AESilky/sd-zmb/hw/SD-ZMB/Docs/CLK_to_CLK2-IOop-timing.PDF

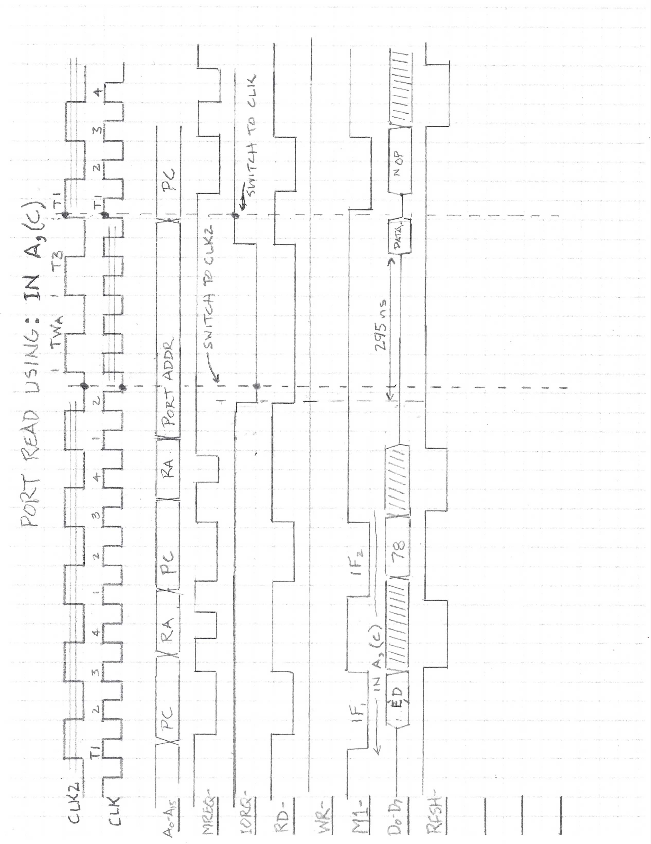
[picture p2: page 1]
