AESilky/sd-zmb/hw/SD-ZMB/Docs/CLK_to_CLK2-timing.PDF

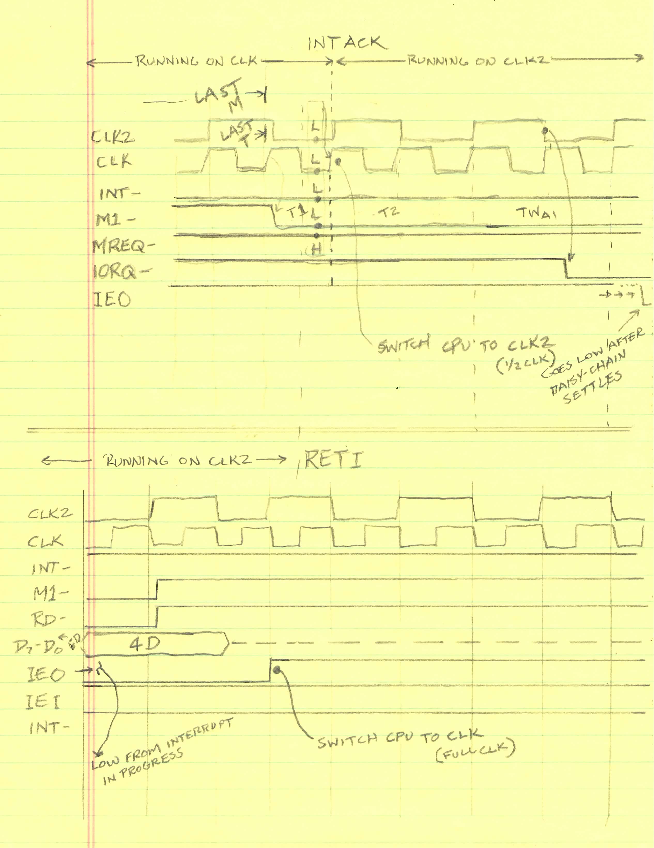
[picture p3: page 1]
