AESilky/sd-zmb/hw/SD-ZMB/Docs/Z80-INTACK-6vs12MHz-AddWS.pdf

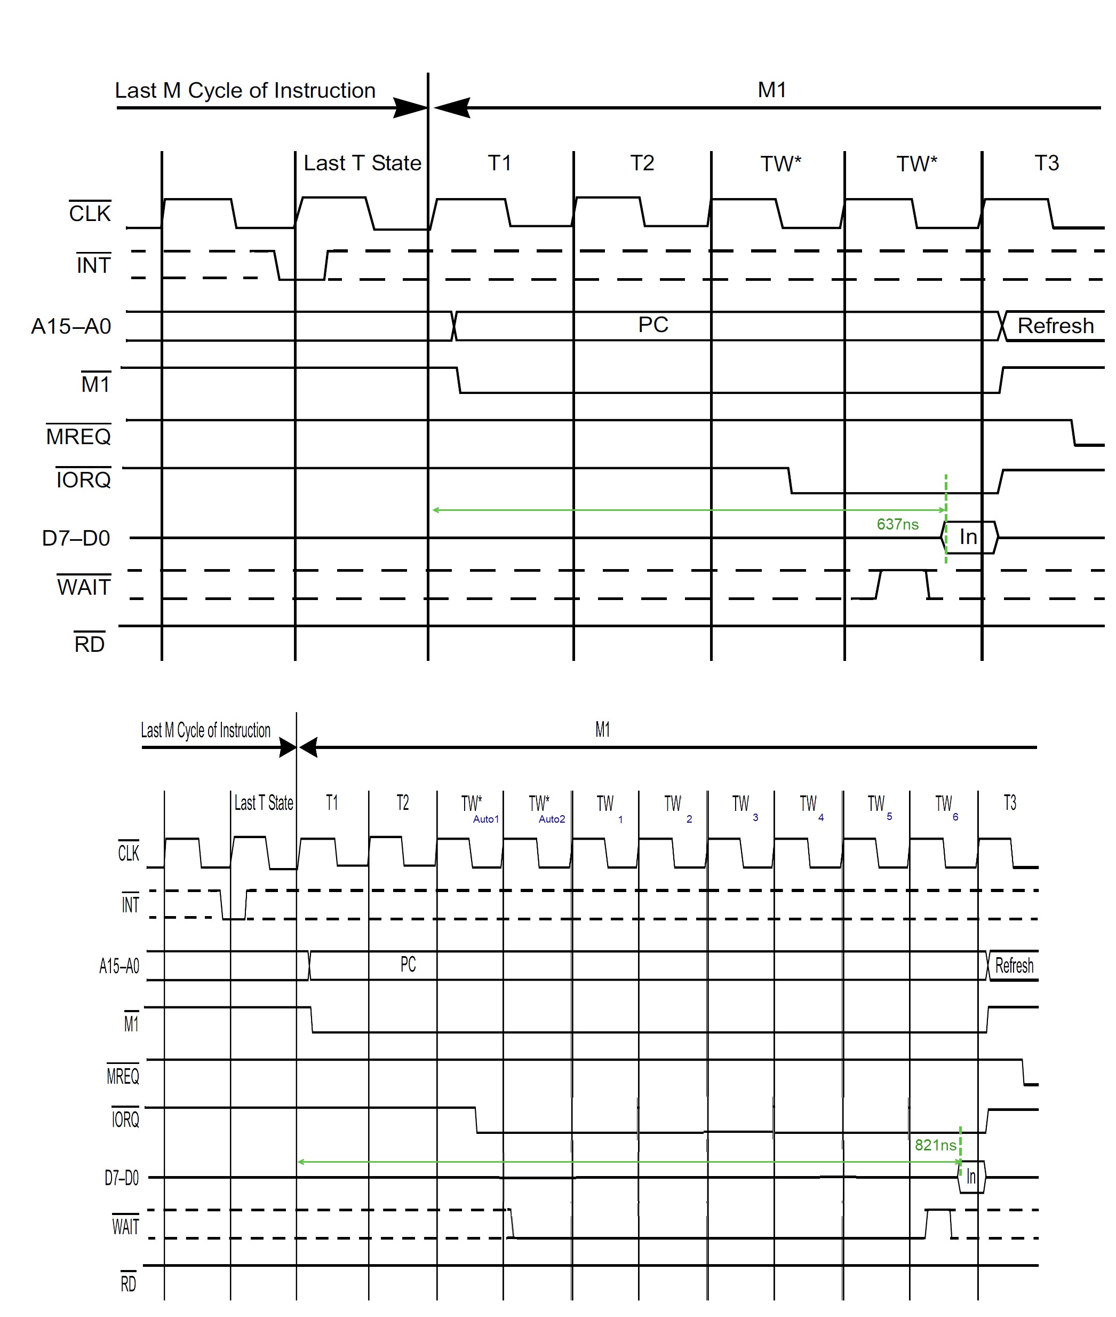
[picture p4: page 1]
