AESilky/sd-zmb/hw/SD-ZMB/Docs/Z80-IO-6vs12MHz-AddWS.pdf

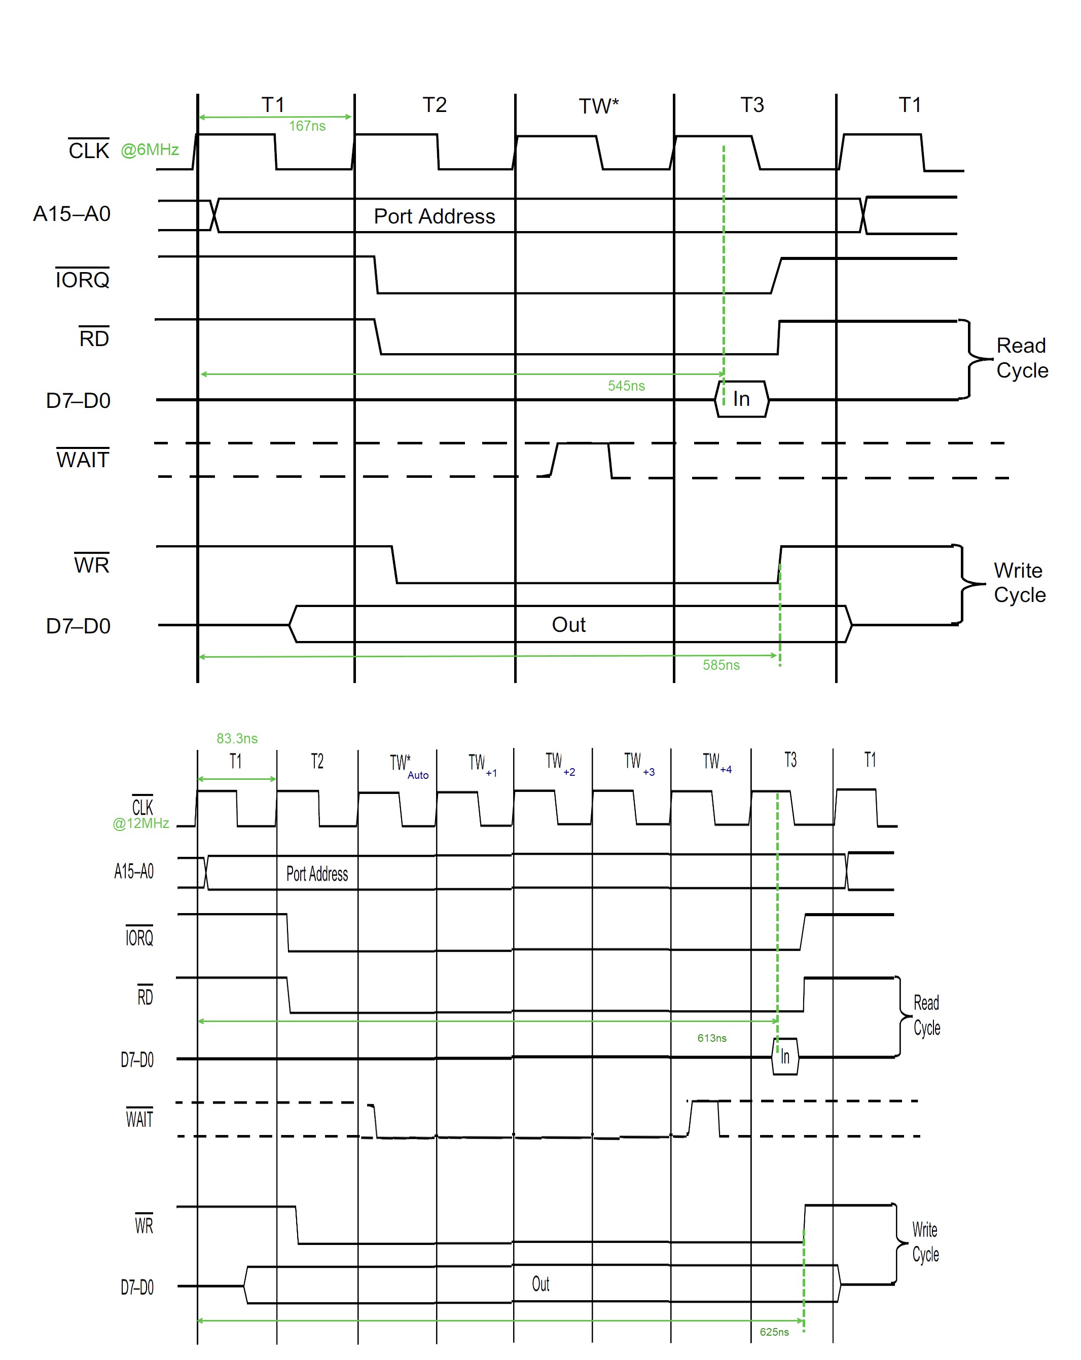
[picture p5: page 1]
