AESilky/sd-zmb/hw/SD-ZMB/Docs/Z80-IO-timing-ws.pdf

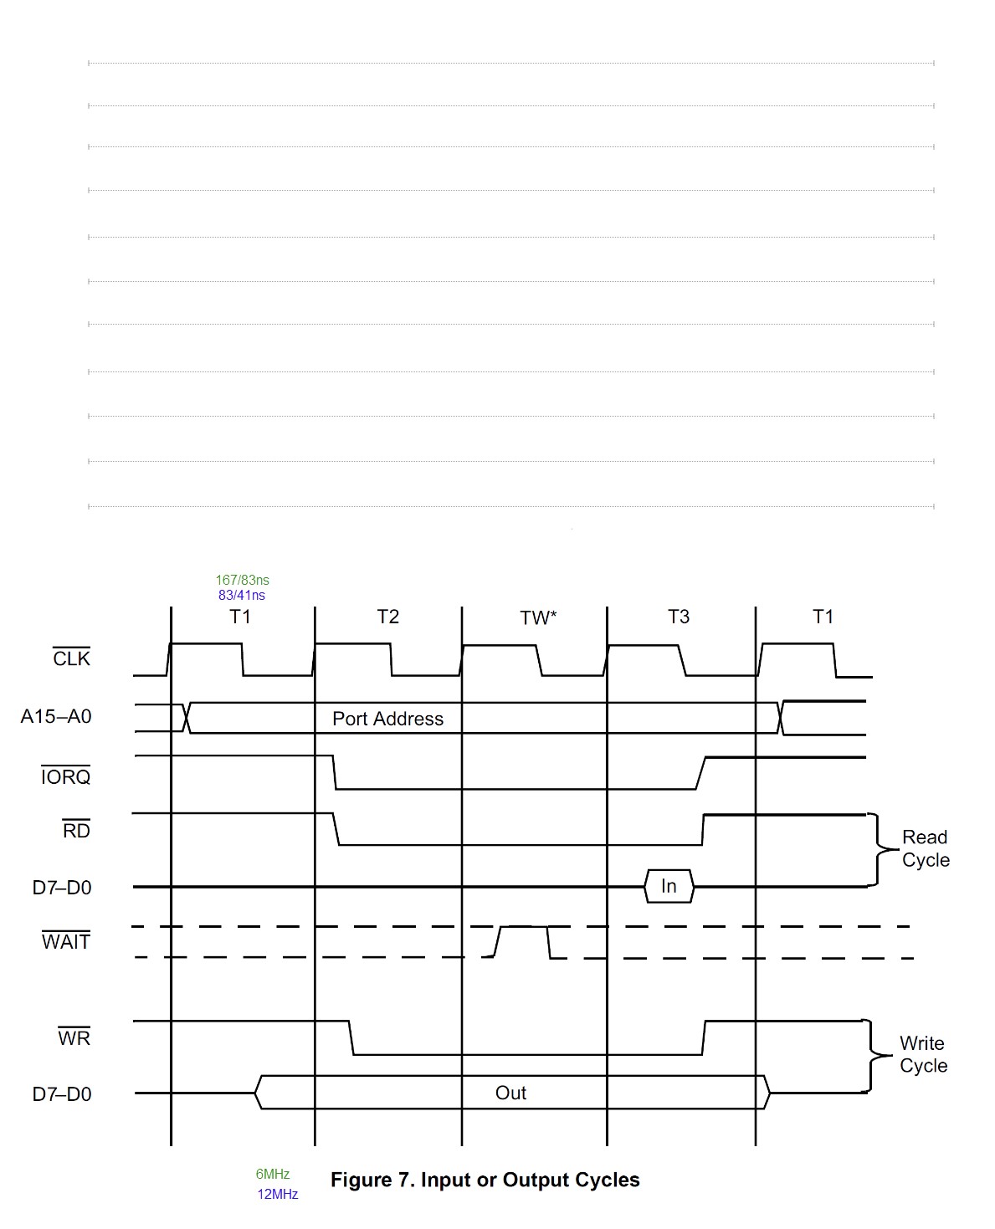
[picture p6: page 1]
