AESilky/sd-zmb/hw/SD-ZMB/Plot/SD-MSZ.pdf

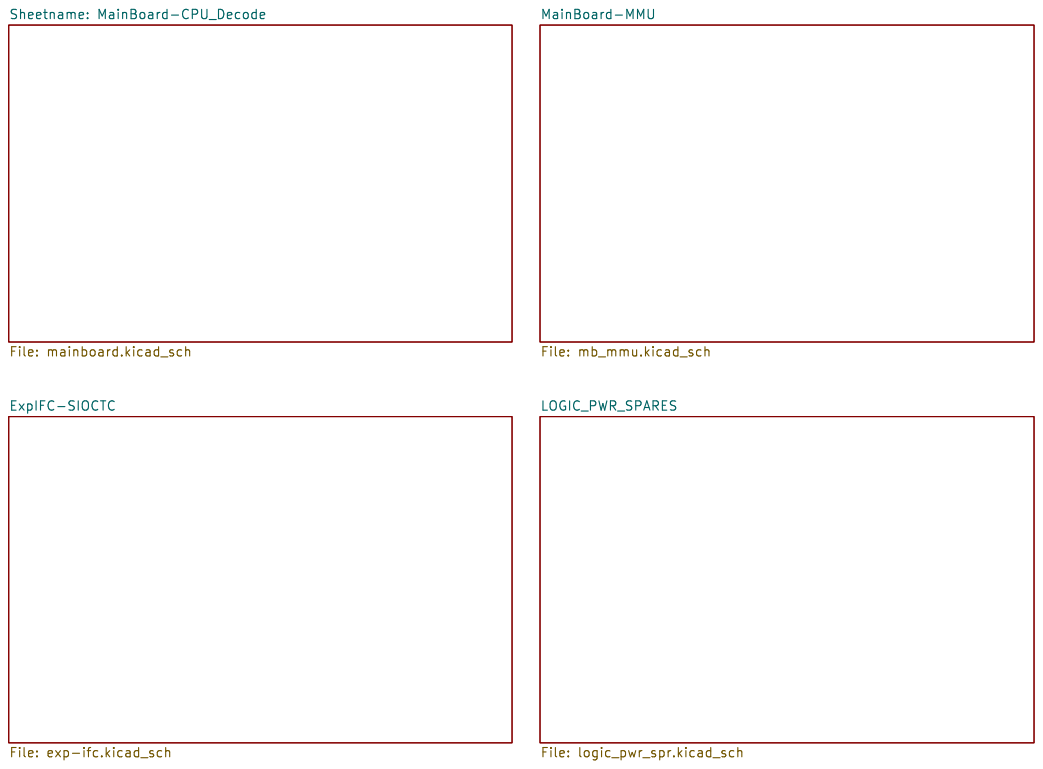
[picture p18: page 1]

File: SD-MSZ.kicad_sch Sheet: / SilkyDESIGN

Id: 1/5 Title: MicroSystem Z80 w/Front Panel & RC2014 Bus

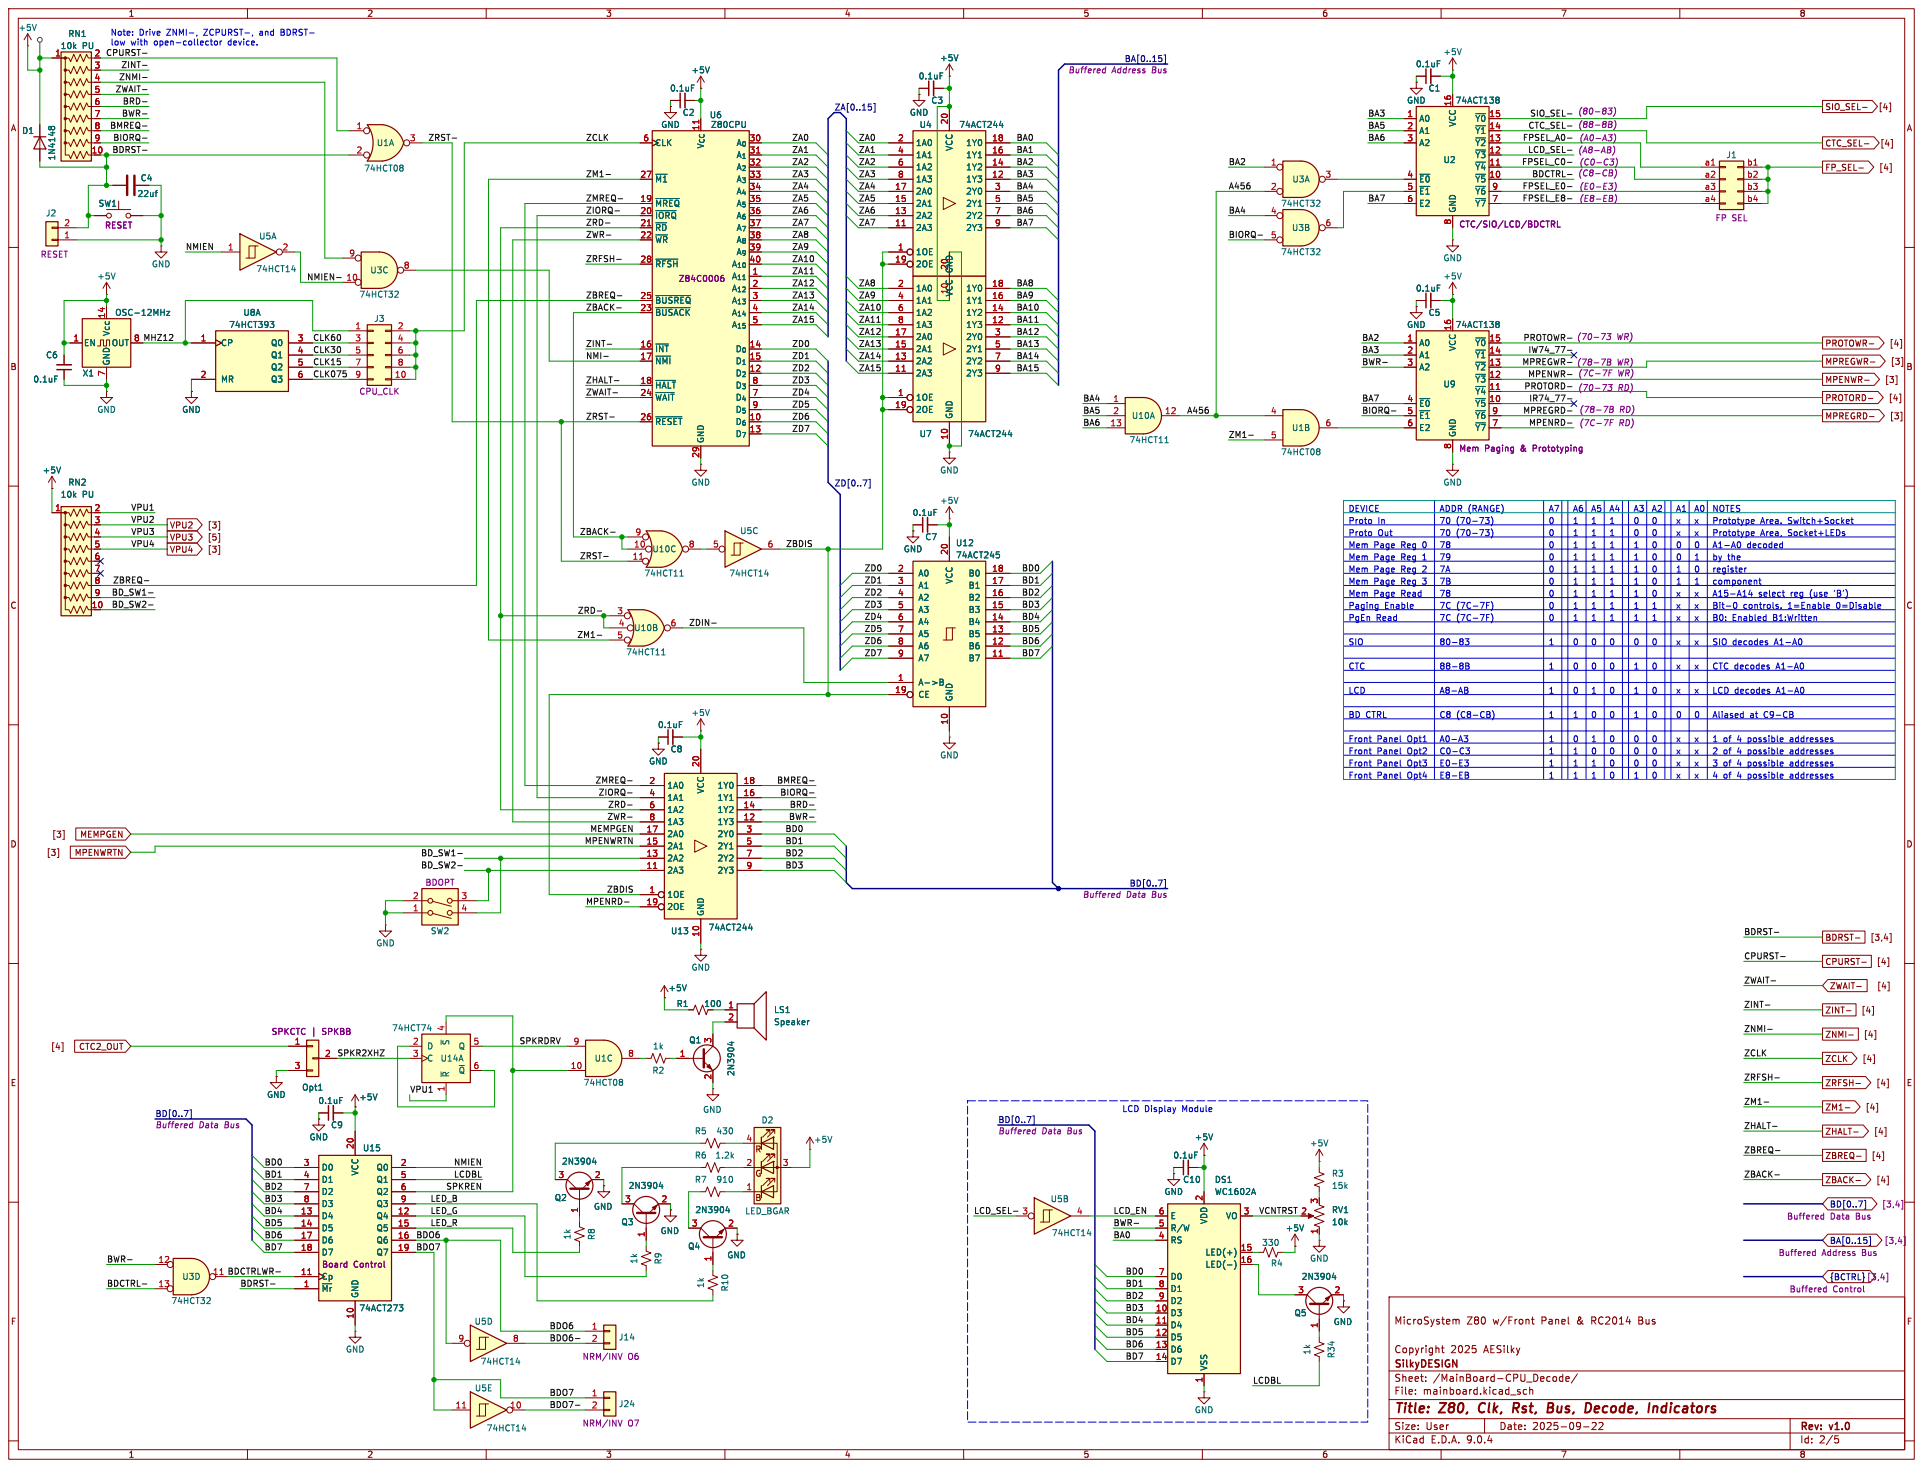
[picture p19: page 2]

74ACT138 CTC/SIO/LCD/BDCTRL +5V

8 ~{Y0}15 ~{Y1}14 ~{Y2}13 ~{Y3}12 ~{Y4}11 ~{Y5}10 ~{Y6}9 ~{Y7}7 X1 OSC-12MHz EN 1 Vcc 14 GND

ZWAIT- ZRST- NMI- ZHALT-

BD7 BD5 BD[0..7] Buffered Data Bus BD5 BD4

BD2 BD[0..7] Buffered Data Bus

SilkyDESIGN
File: mainboard.kicad_sch Sheet: /MainBoard-CPU_Decode/
Id: 2/5 Title: Z80, Clk, Rst, Bus, Decode, Indicators

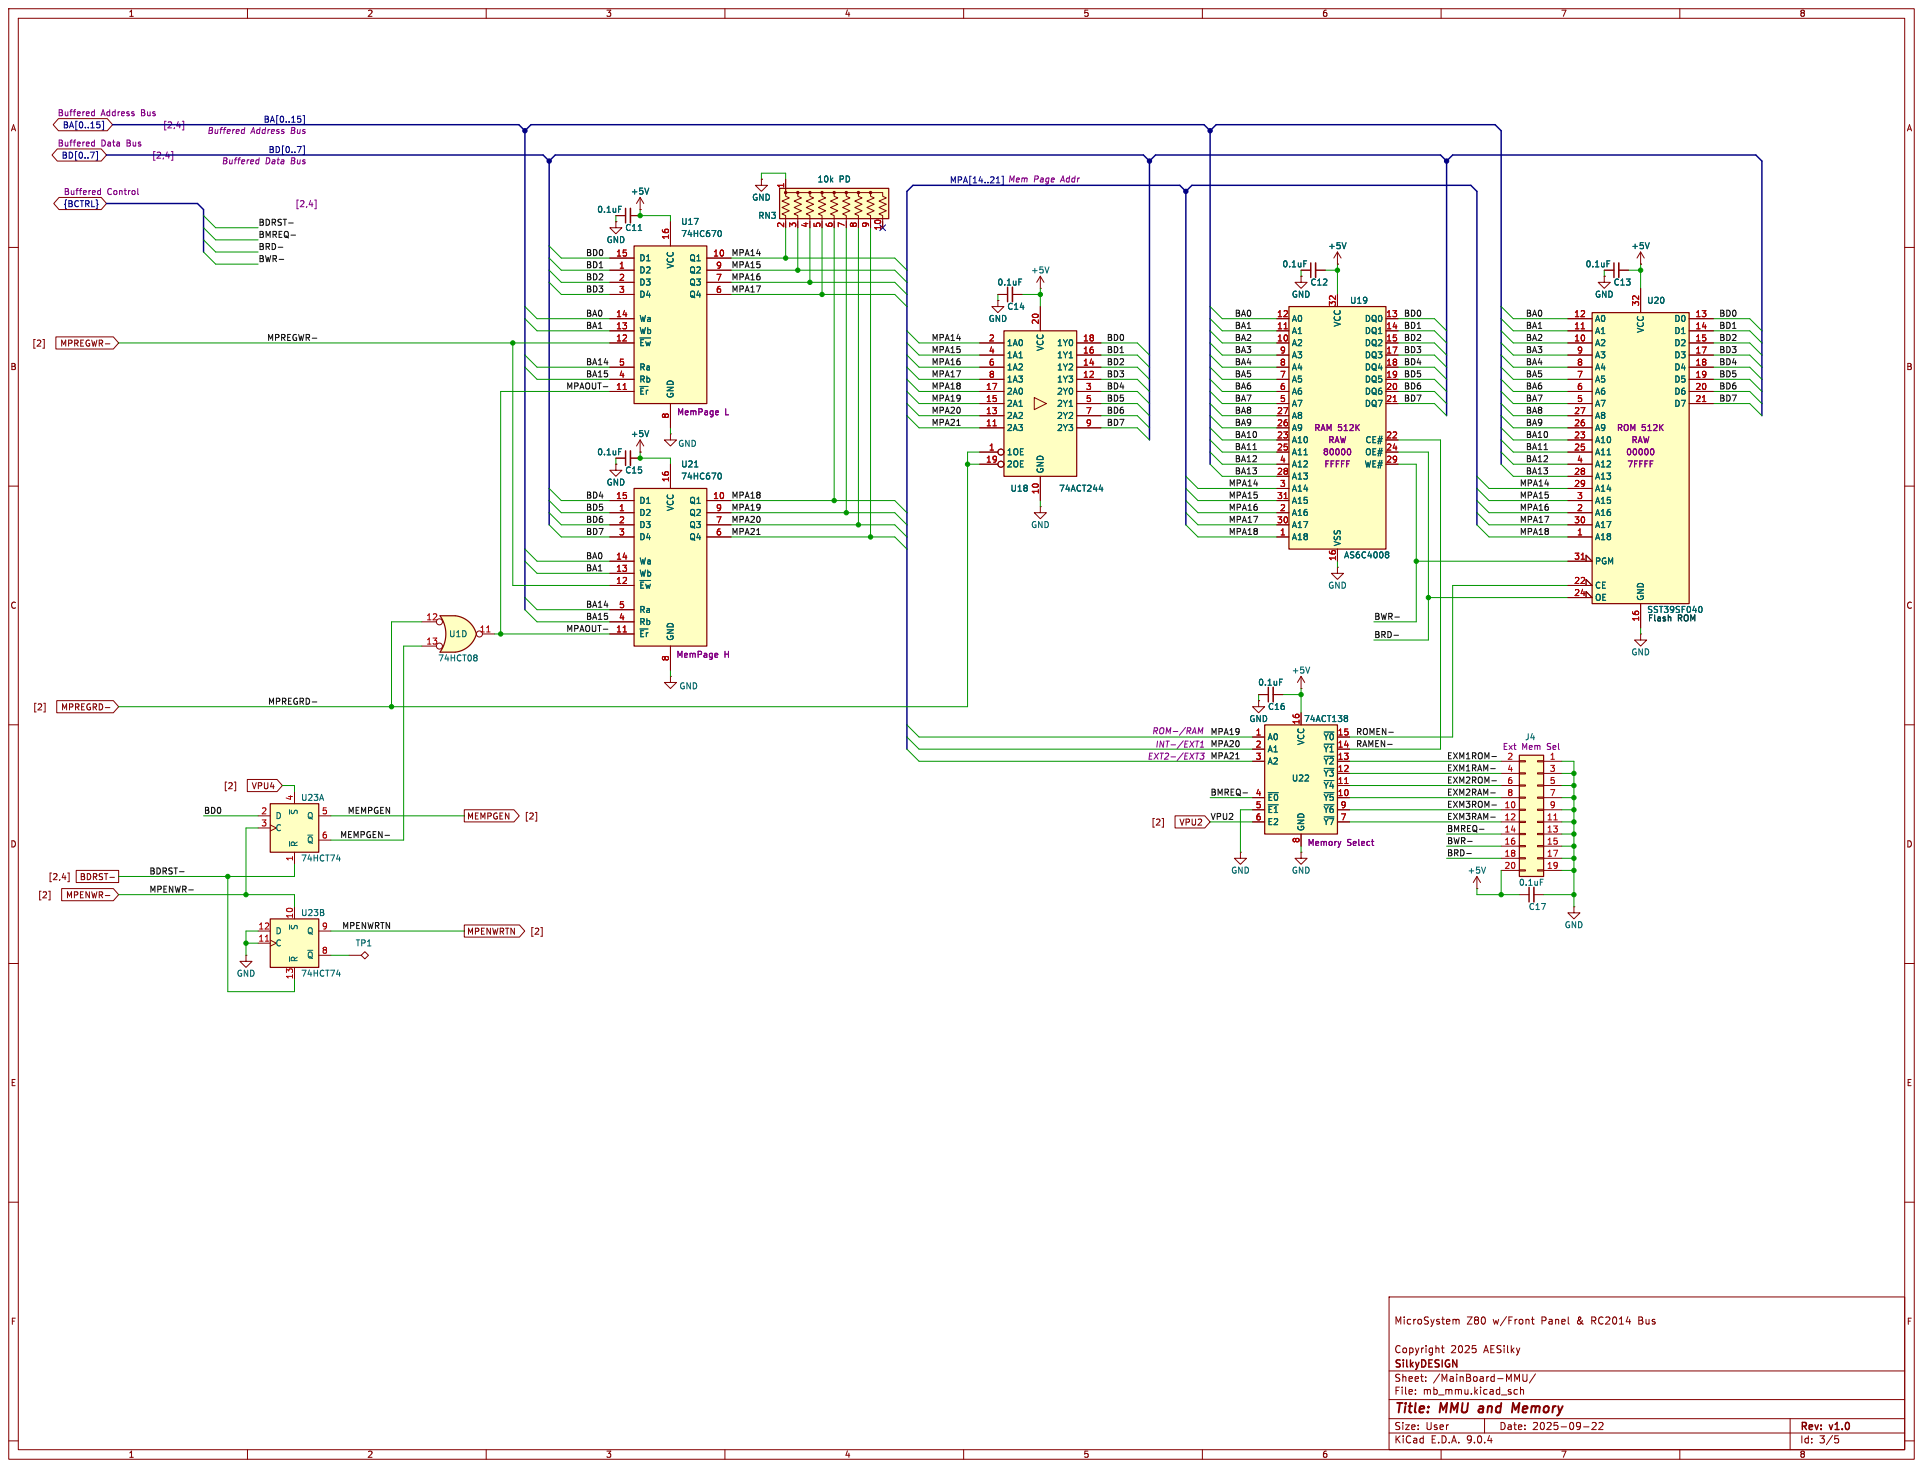
[picture p20: page 3]

MPREGWR- BA[0..15] Buffered Address Bus

File: mb_mmu.kicad_sch Sheet: /MainBoard-MMU/ SilkyDESIGN

Id: 3/5 Title: MMU and Memory

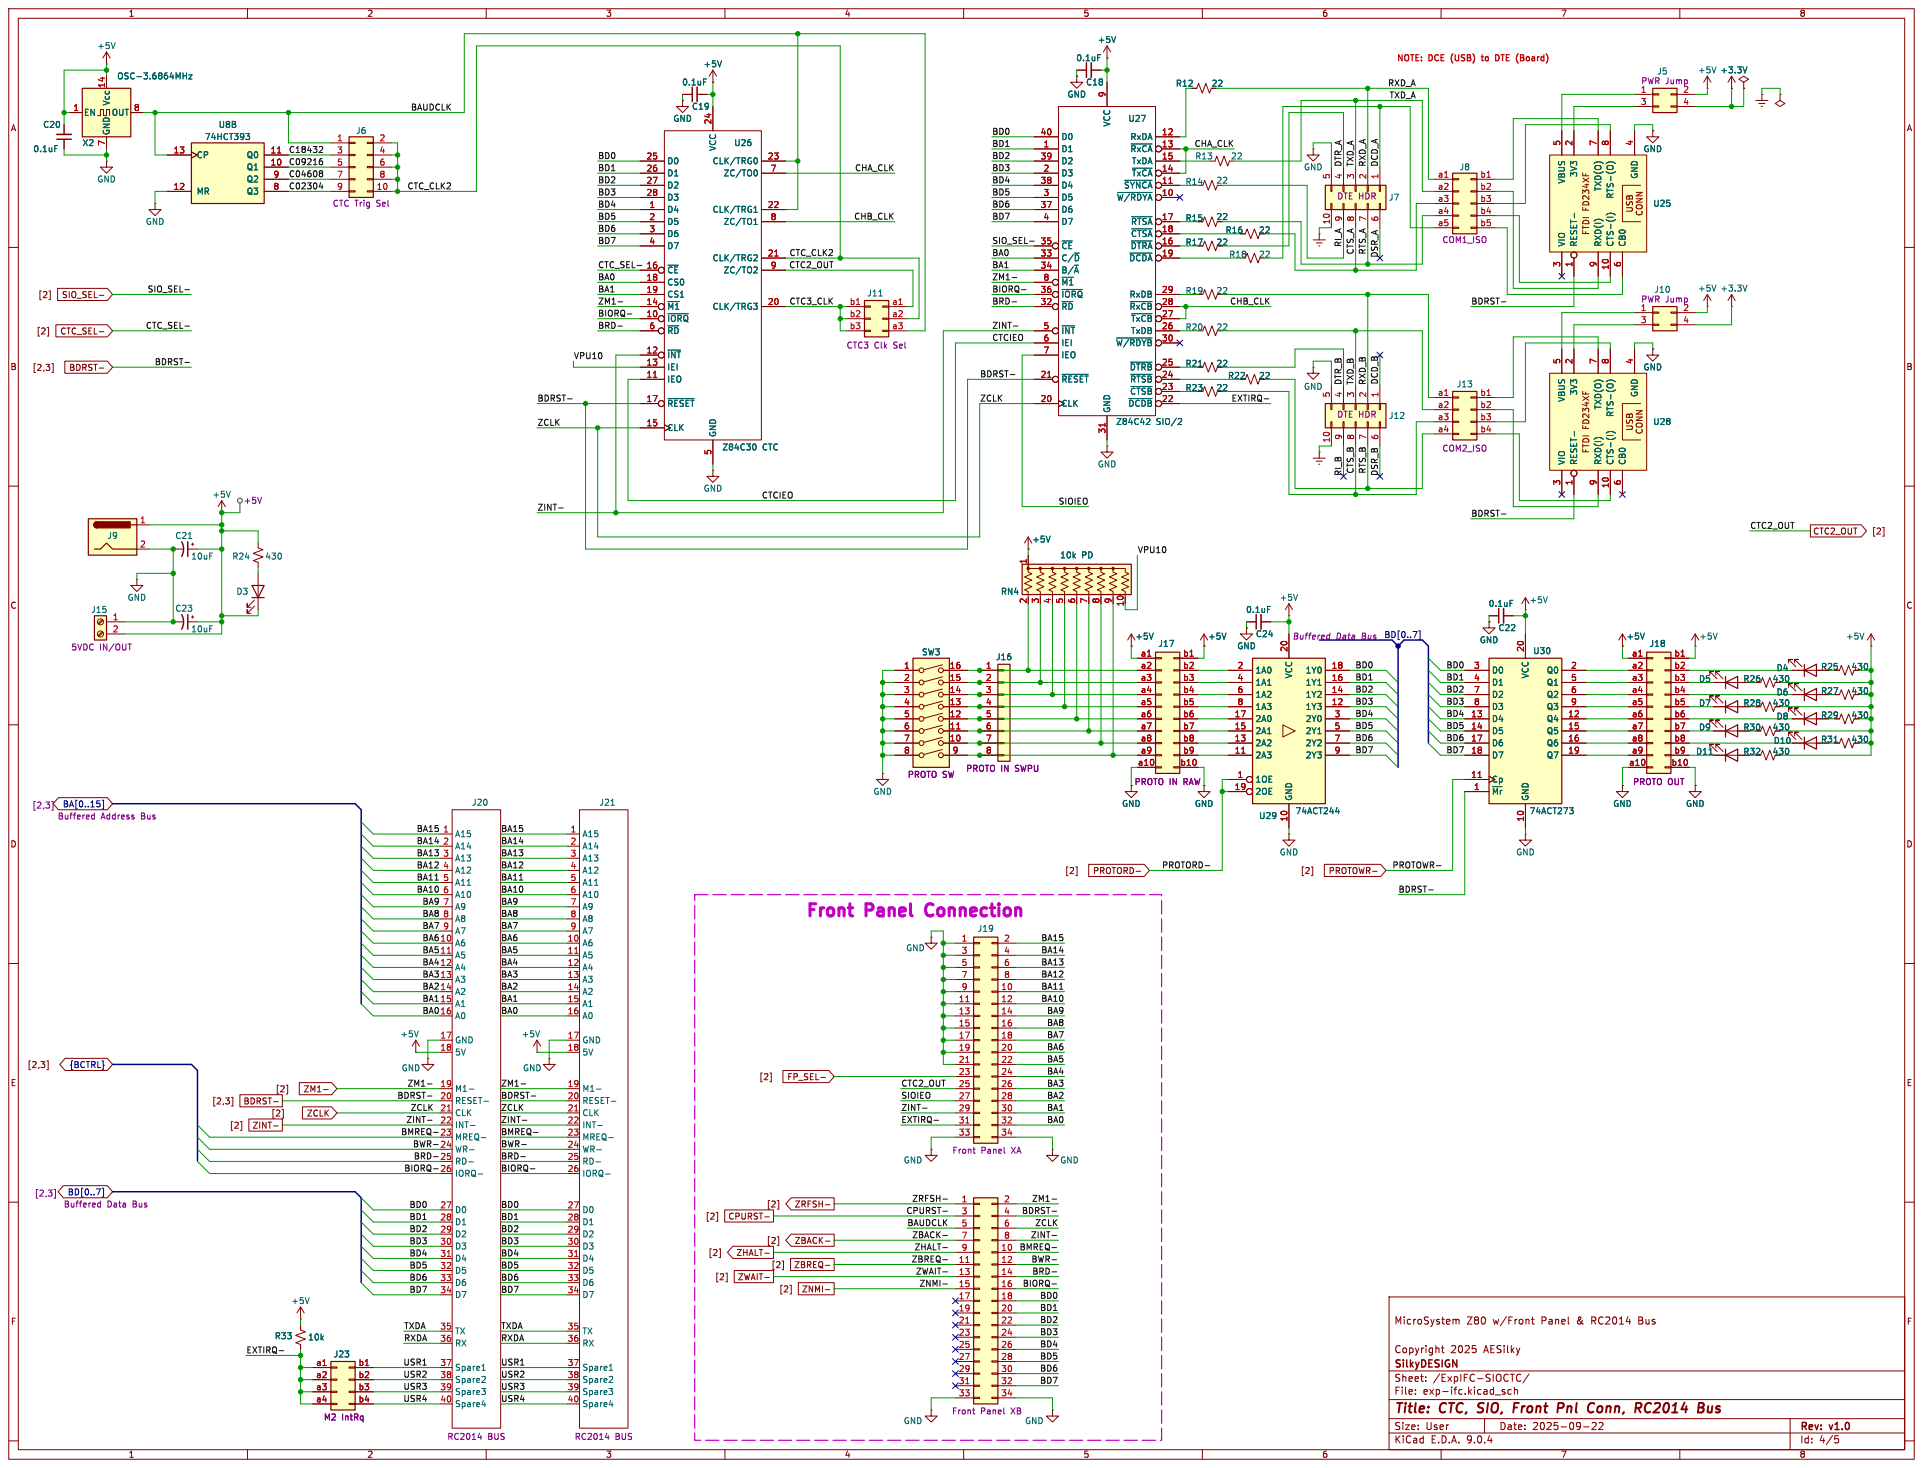
[picture p21: page 4]

NOTE: DCE (USB) to DTE (Board)

9 GND 31 RxDA 12 ~{RxCA}13 TxDA 15 ~{TxCA}14 ~{SYNCA}11 ~{W/RDYA}10 ~{RTSA}17 ~{CTSA}18 ~{DTRA}16 ~{DCDA}19 RxDB 29 ~{RxCB}28 ~{TxCB}27 TxDB 26 ~{W/RDYB} 30 ~{DTRB}25 ~{RTSB}24 ~{CTSB}23 ~{DCDB}22 U27 Z84C42 SIO/2 GND FTDI FD234XF USB

9 GND 31 RxDA 12 ~{RxCA}13 TxDA 15 ~{TxCA}14 ~{SYNCA}11 ~{W/RDYA}10 ~{RTSA}17 ~{CTSA}18 ~{DTRA}16 ~{DCDA}19 RxDB 29 ~{RxCB}28 ~{TxCB}27 TxDB 26 ~{W/RDYB} 30 ~{DTRB}25 ~{RTSB}24 ~{CTSB}23 ~{DCDB}22 GND GND

5 CLK/TRG0 23 ZC/TO0 7 CLK/TRG1 22 ZC/TO1 8 CLK/TRG2 21 ZC/TO2 9 CLK/TRG3 20 U26 Z84C30 CTC

5 CLK/TRG0 23 ZC/TO0 7 CLK/TRG1 22 ZC/TO1 8 CLK/TRG2 21 ZC/TO2 9 CLK/TRG3 20 C22

Buffered Data Bus BD[0..7] BD1

BD6 BDRST- PROTOWR- BD5 BD4 BD3 ZINT- BWR- BDRST- ZCLK

[2] FP_SEL- BA[0..15] [2,3] Buffered Address Bus

INT- 22 MREQ- 23 WR- 24 RD- 25

SilkyDESIGN
File: exp-ifc.kicad_sch Sheet: /ExpIFC-SIOCTC/
Id: 4/5 Title: CTC, SIO, Front Pnl Conn, RC2014 Bus

34 Front Panel XB GND

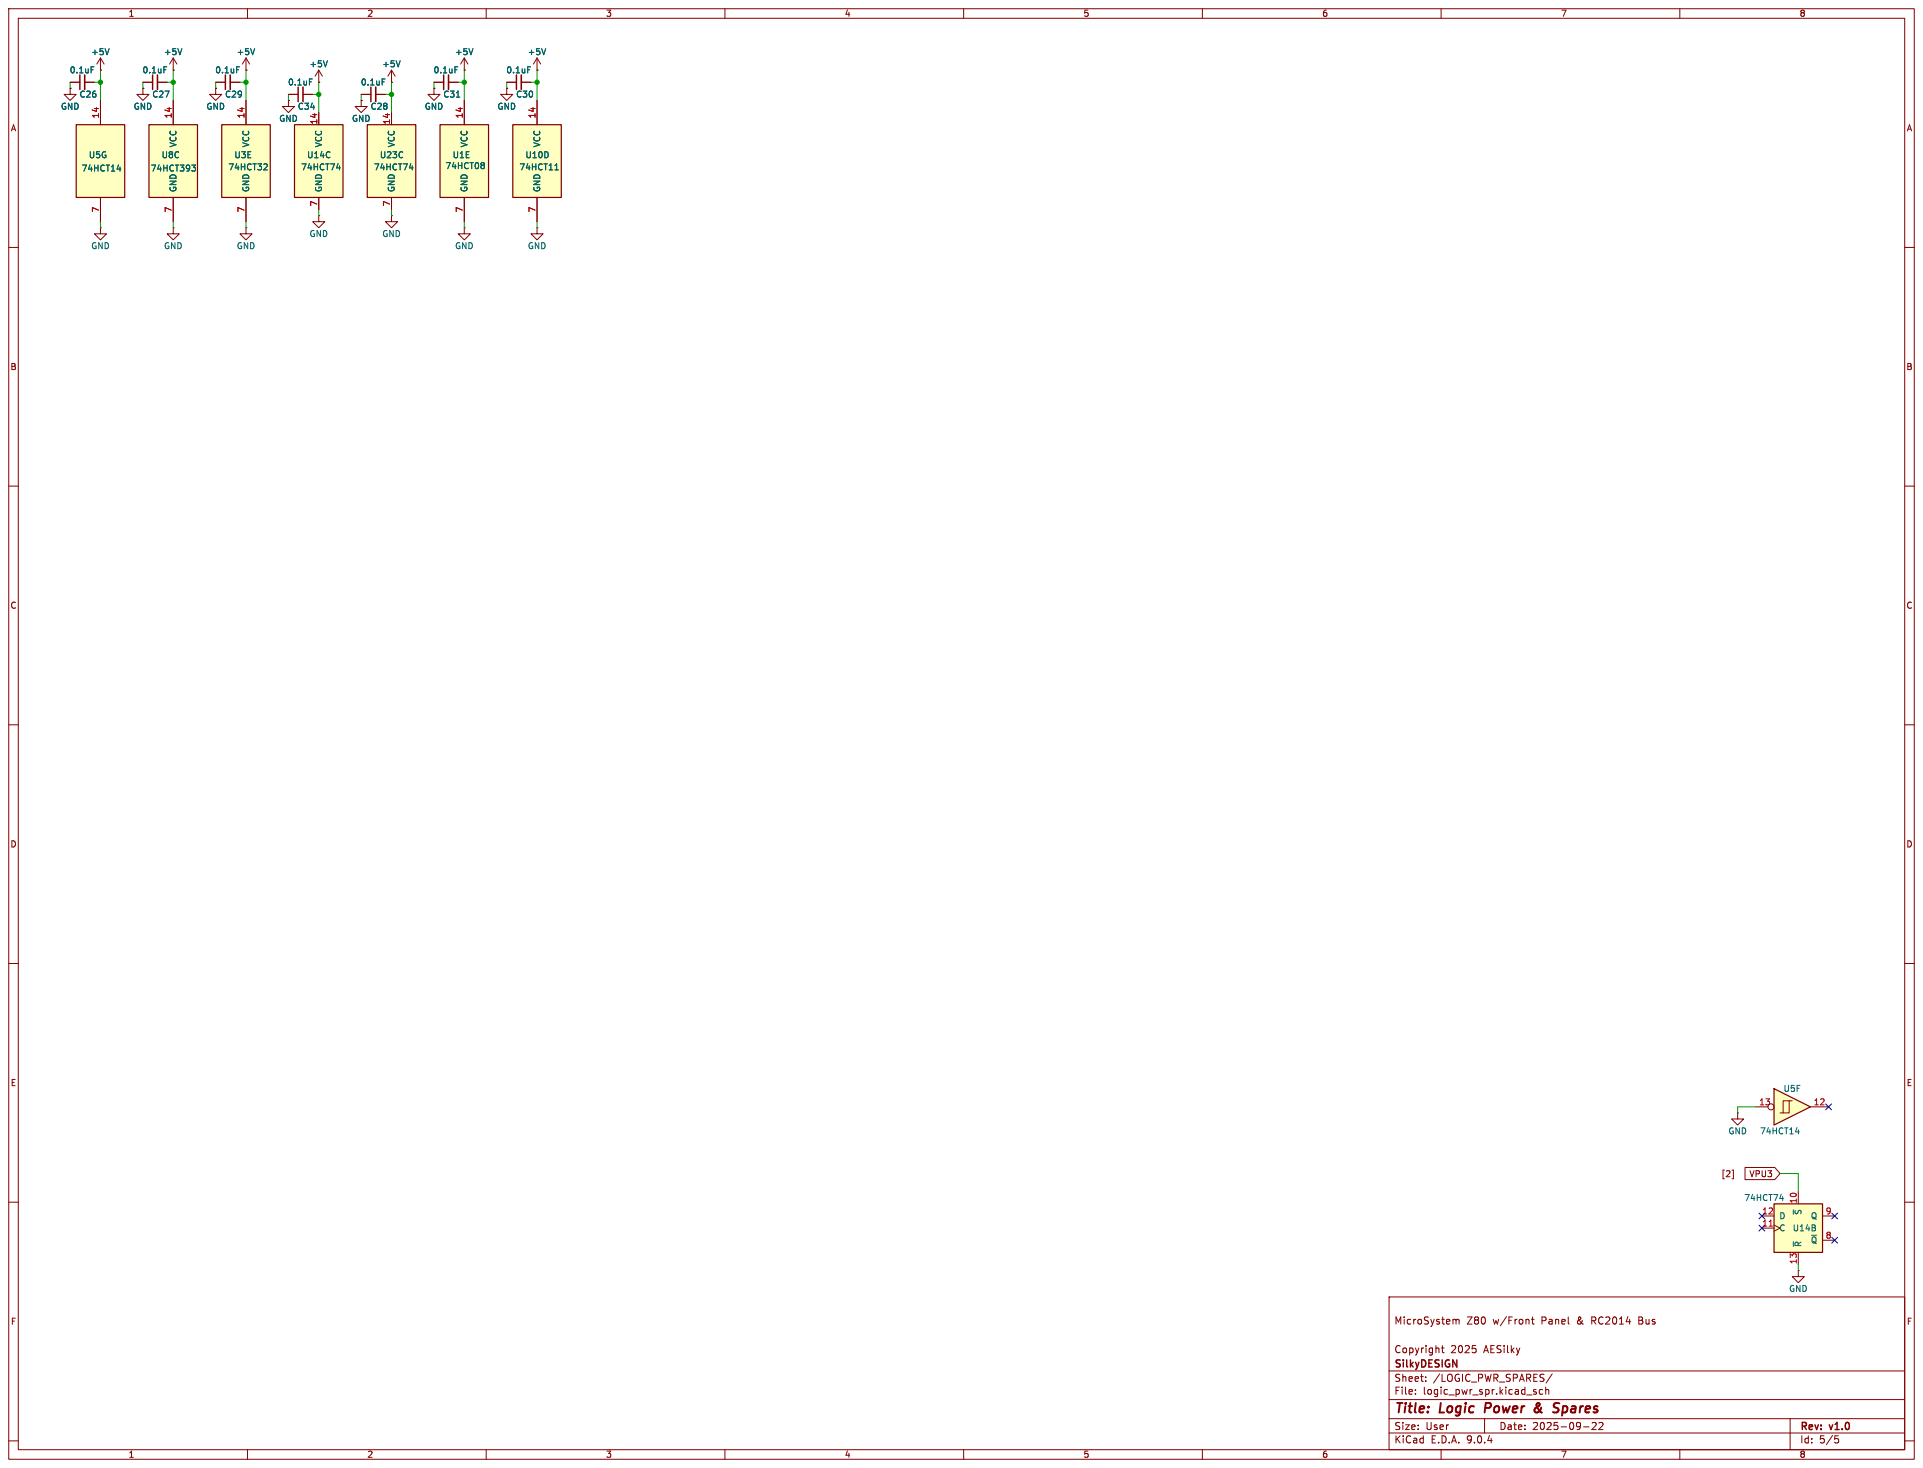
[picture p22: page 5]

SilkyDESIGN
File: logic_pwr_spr.kicad_sch Sheet: /LOGIC_PWR_SPARES/
Id: 5/5 Title: Logic Power & Spares
