AESilky/sd-zmb/hw/SD-ZMB/Plot/ZMB-PCB_PR8_2.pdf

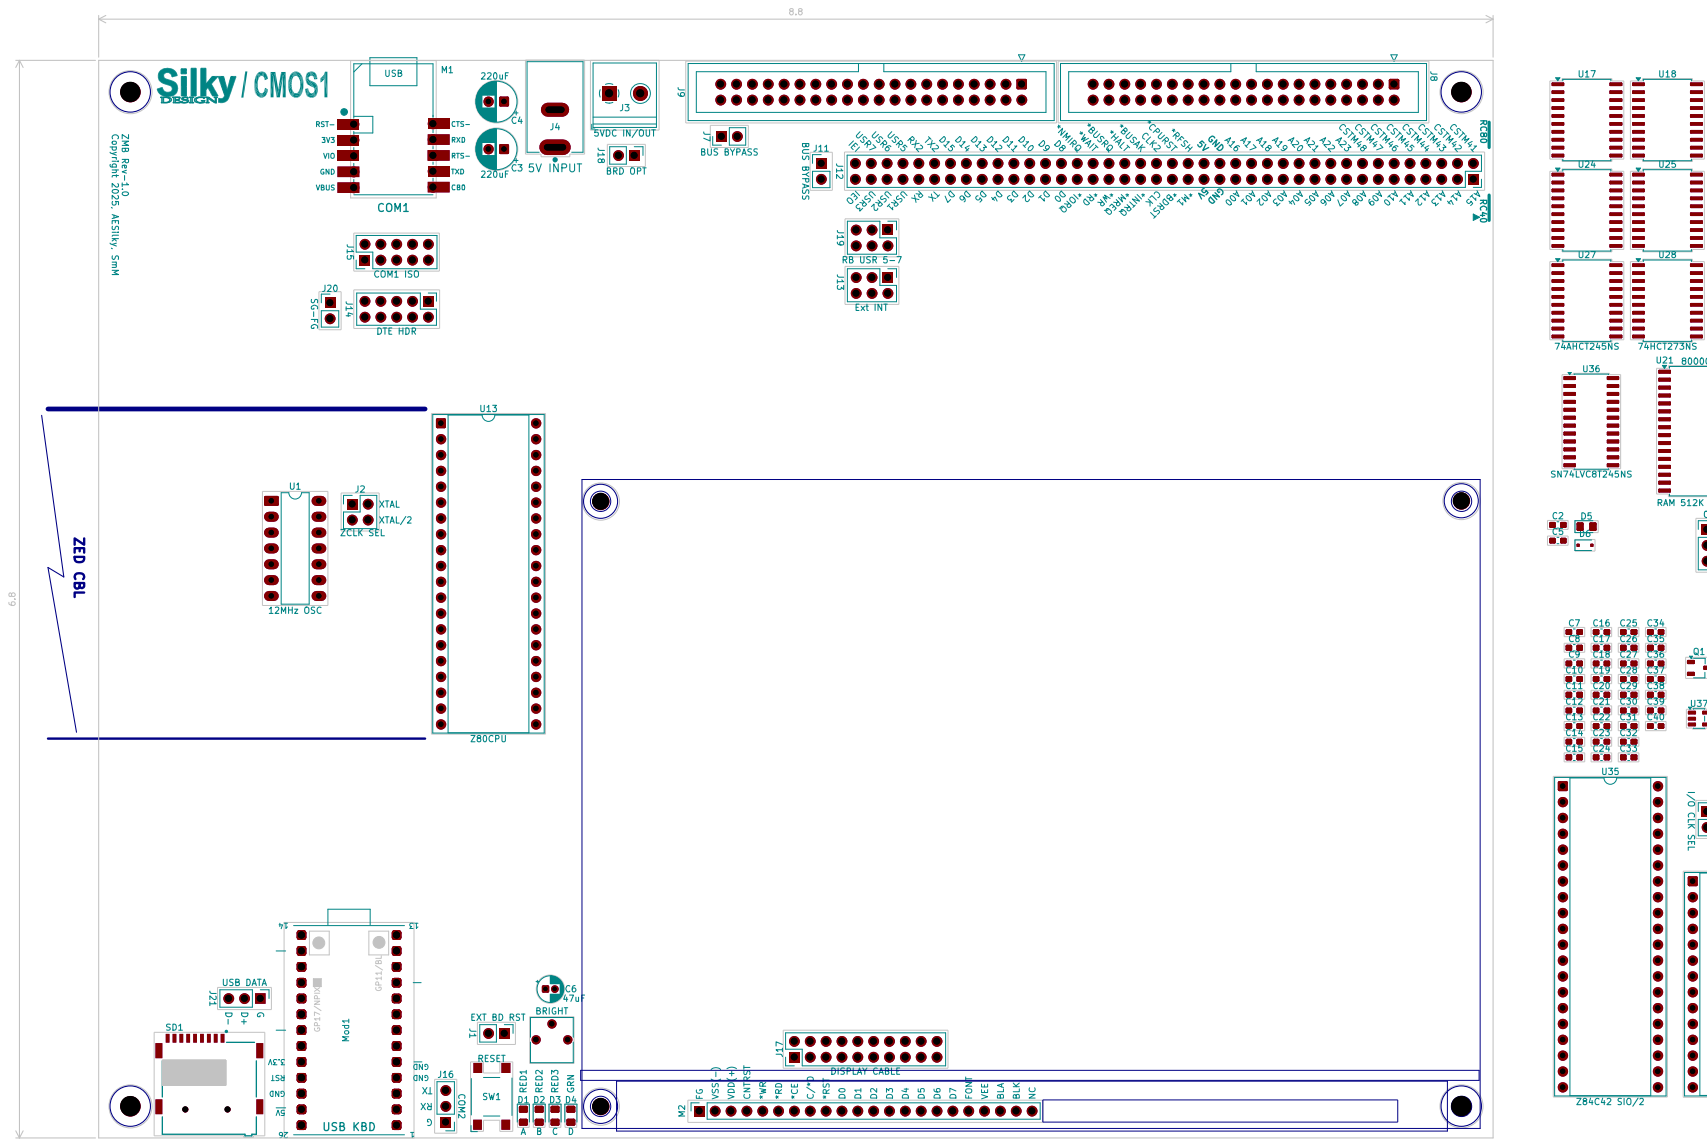
[picture p34: page 1]
